FablabTorino/tinyMatrix/design/pendant/2.png

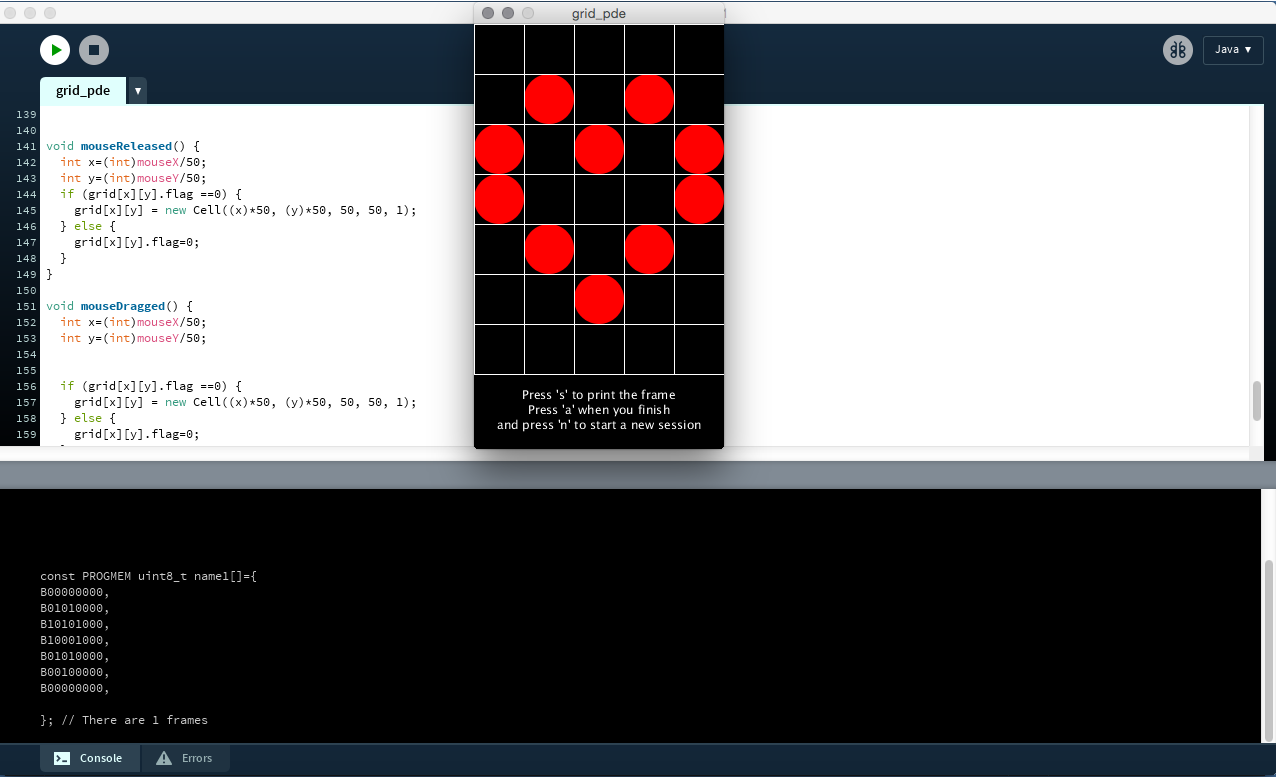
design/pendant/2.png
