FablabTorino/tinyMatrix/design/pendant/back-cover.jpg

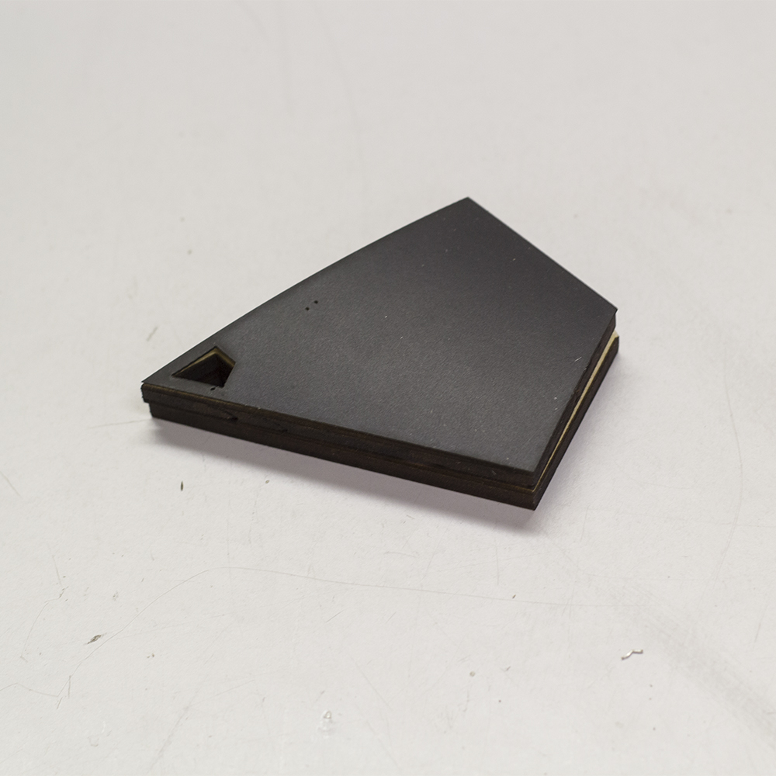
design/pendant/back-cover.jpg
