FablabTorino/tinyMatrix/design/pendant/Saldature.jpg

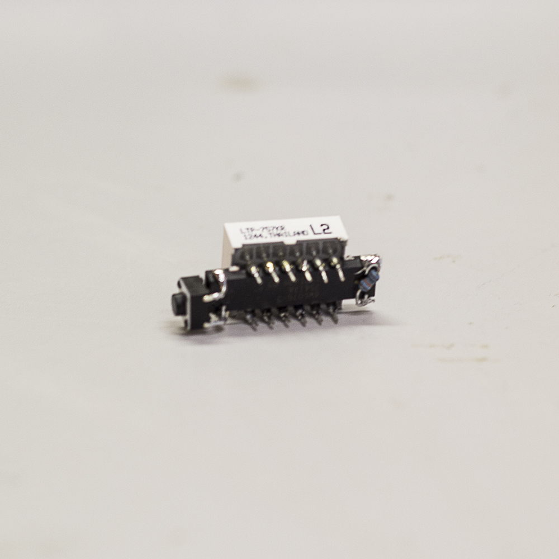
design/pendant/Saldature.jpg
