FablabTorino/tinyMatrix/design/pendant/shield.jpg

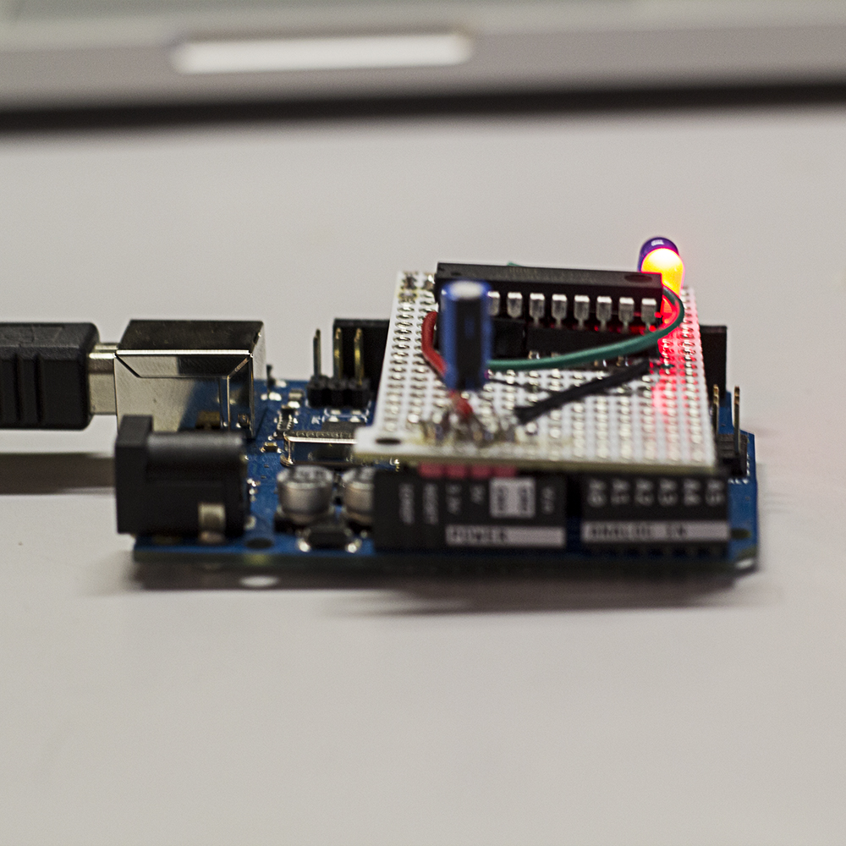
design/pendant/shield.jpg
