FablabTorino/tinyMatrix/code/arduino programming/LedMatrix_ATtiny /Images.h

const PROGMEM uint8_t vertigo[]={
B10000000,
B00000000,
B00000000,
B00000000,
B00000000,
B00000000,
B00000000,

B10000000,
B10000000,
B00000000,
B00000000,
B00000000,
B00000000,
B00000000,

B10000000,
B10000000,
B10000000,
B00000000,
B00000000,
B00000000,
B00000000,

B10000000,
B10000000,
B10000000,
B10000000,
B00000000,
B00000000,
B00000000,

B10000000,
B10000000,
B10000000,
B10000000,
B10000000,
B00000000,
B00000000,

B10000000,
B10000000,
B10000000,
B10000000,
B10000000,
B10000000,
B00000000,

B10000000,
B10000000,
B10000000,
B10000000,
B10000000,
B10000000,
B10000000,

B10000000,
B10000000,
B10000000,
B10000000,
B10000000,
B10000000,
B11000000,

B10000000,
B10000000,
B10000000,
B10000000,
B10000000,
B10000000,
B11100000,

B10000000,
B10000000,
B10000000,
B10000000,
B10000000,
B10000000,
B11110000,

B10000000,
B10000000,
B10000000,
B10000000,
B10000000,
B10000000,
B11111000,

B10000000,
B10000000,
B10000000,
B10000000,
B10000000,
B10001000,
B11111000,

B10000000,
B10000000,
B10000000,
B10000000,
B10001000,
B10001000,
B11111000,

B10000000,
B10000000,
B10000000,
B10001000,
B10001000,
B10001000,
B11111000,

B10000000,
B10000000,
B10001000,
B10001000,
B10001000,
B10001000,
B11111000,

B10000000,
B10001000,
B10001000,
B10001000,
B10001000,
B10001000,
B11111000,

B10001000,
B10001000,
B10001000,
B10001000,
B10001000,
B10001000,
B11111000,

B10011000,
B10001000,
B10001000,
B10001000,
B10001000,
B10001000,
B11111000,

B10111000,
B10001000,
B10001000,
B10001000,
B10001000,
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
B00000000,
B00000000,
B00000000,
B00000000,
B00000000,

B11000000,
B00000000,
B00000000,
B00000000,
B00000000,
B00000000,
B00000000,

B10000000,
B00000000,
B00000000,
B00000000,
B00000000,
B00000000,
B00000000,

B00000000,
B00000000,
B00000000,
B00000000,
B00000000,
B00000000,
B00000000,

};
